ViperWorx/AX-02/Images/AX-02_2.png

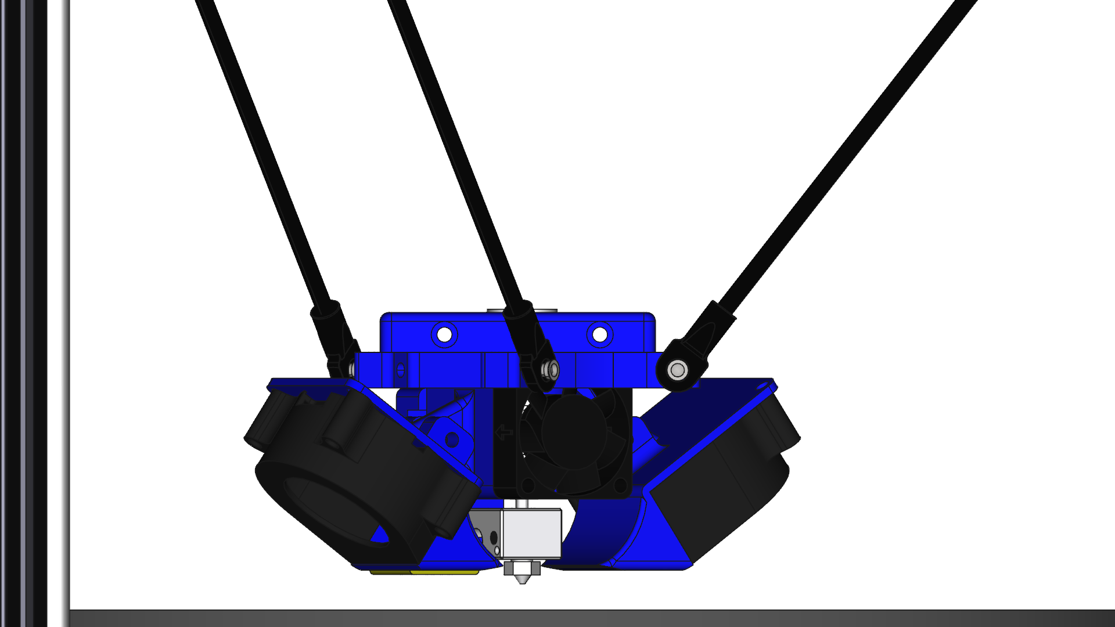
Images/AX-02_2.png
