ViperWorx/AX-02/Images/AX-02_4.png

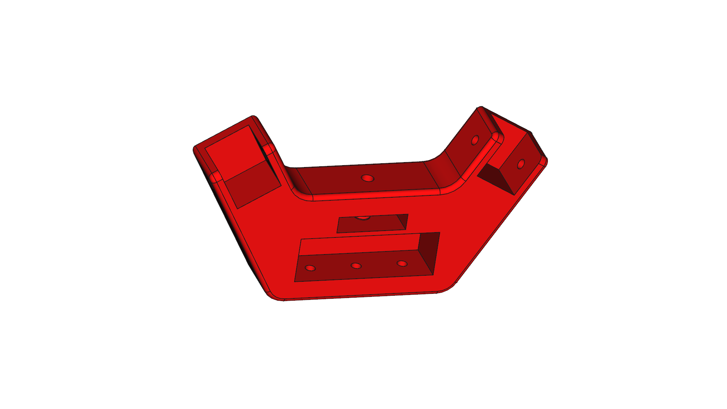
Images/AX-02_4.png
