ViperWorx/AX-02/FreeCAD/STEP/Hardware Parts/Build_plate.step

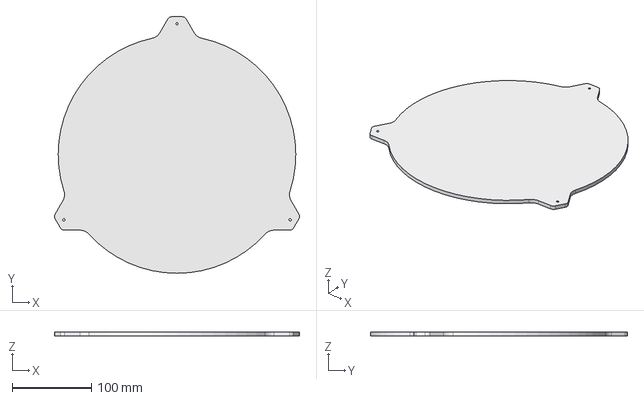
[picture p24: CAD file, 2017-04-28]
FreeCAD/STEP/Hardware Parts/Build_plate.step
309.3 x 323.9 x 5.00 mm
