ViperWorx/AX-02/FreeCAD/STEP/Printed Parts/Top_Bracket.step

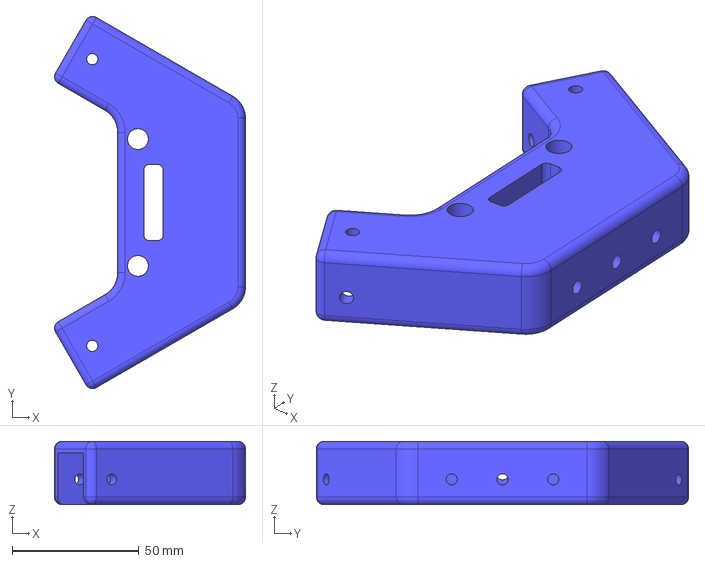
[picture p25: CAD file, 2017-02-15]
FreeCAD/STEP/Printed Parts/Top_Bracket.step
75.3 x 146.7 x 25.0 mm
