ViperWorx/AX-02/Cover_Plate.dxf

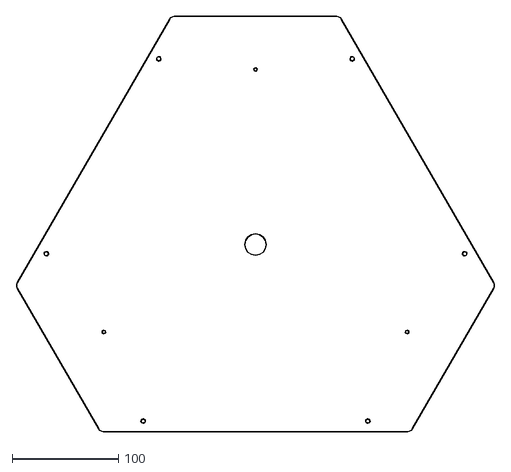
[picture p26: CAD file, 2017-04-28]
Cover_Plate.dxf
450.9 x 391.4
