ViperWorx/AX-02/FreeCAD/Arm_Tensioner.fcstd

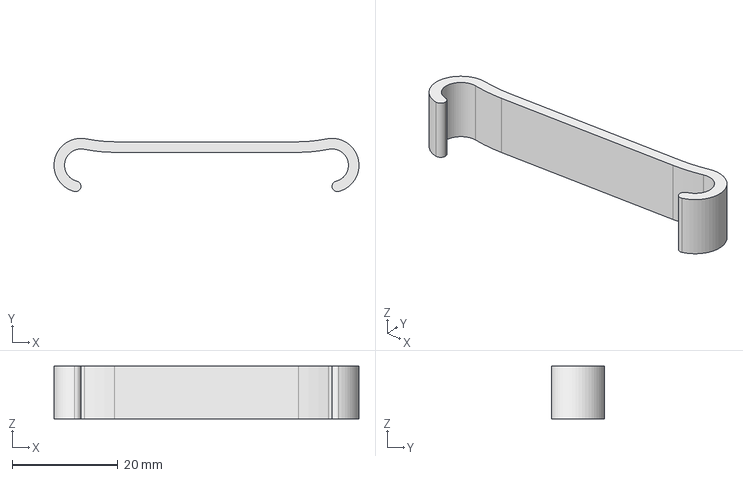
[picture p27: CAD file, 2017-03-06]
FreeCAD/Arm_Tensioner.fcstd
57.7 x 10.1 x 10.0 mm
