ViperWorx/AX-02/FreeCAD/STEP/Printed Parts/Layer_Fan_Mount.step

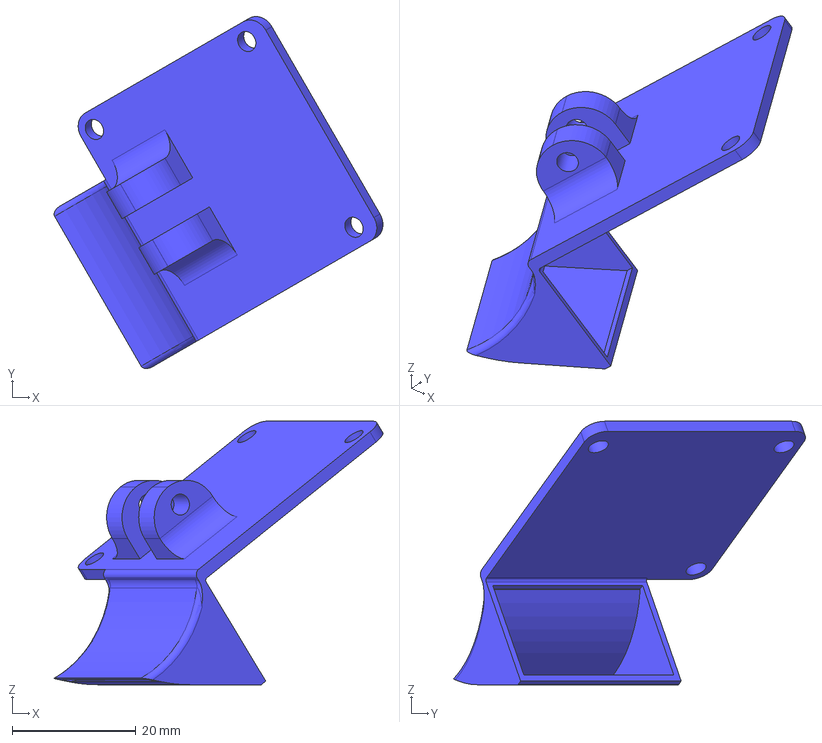
[picture p28: CAD file, 2017-01-31]
FreeCAD/STEP/Printed Parts/Layer_Fan_Mount.step
53.2 x 56.9 x 42.6 mm
