ViperWorx/AX-02/1_Effector.stl

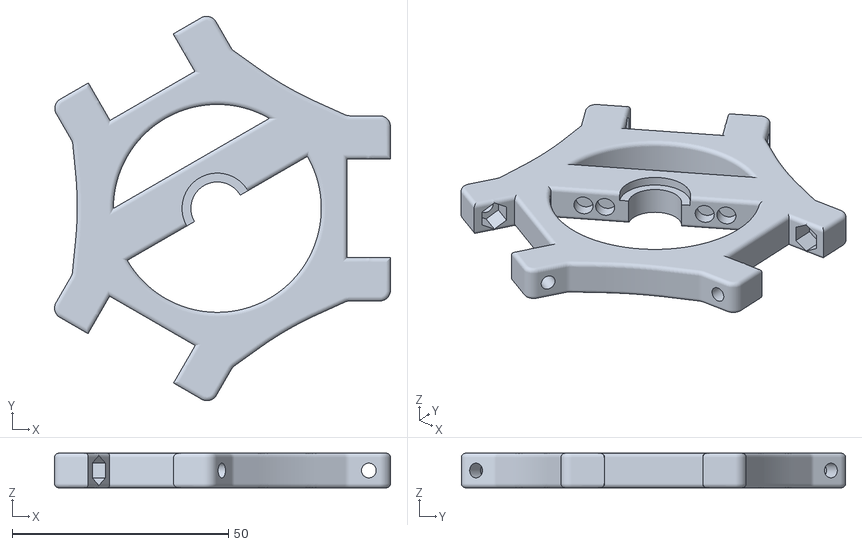
[picture p29: CAD file, 2017-03-30]
1_Effector.stl
77.6 x 88.8 x 8.00
