ViperWorx/AX-02/FreeCAD/Electronics_Plate_Bracket.fcstd

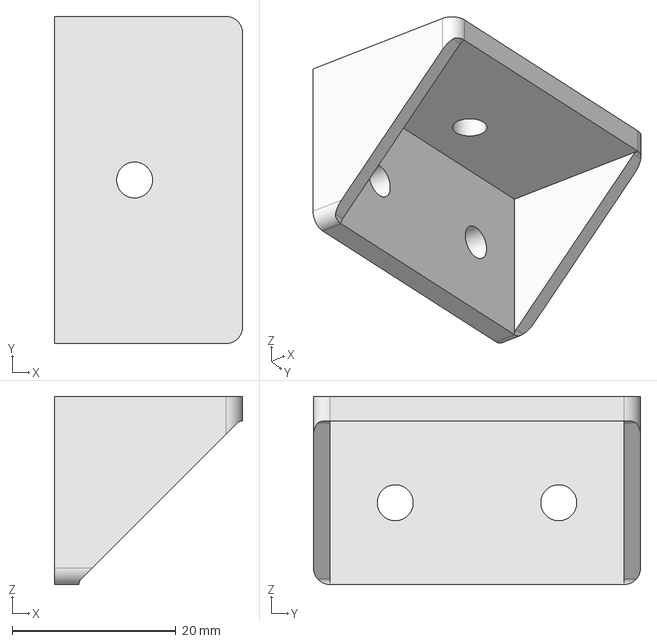
[picture p30: CAD file, 2017-03-06]
FreeCAD/Electronics_Plate_Bracket.fcstd
23.0 x 40.0 x 23.0 mm
