ViperWorx/AX-02/FreeCAD/STEP/Hardware Parts/Cover_Plate.step

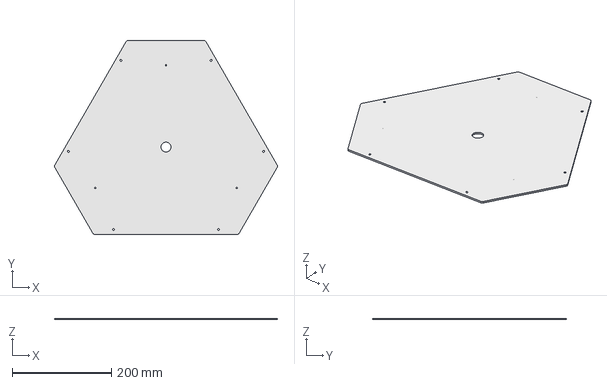
[picture p31: CAD file, 2017-04-28]
FreeCAD/STEP/Hardware Parts/Cover_Plate.step
450.4 x 391.4 x 3.00 mm
