ViperWorx/AX-02/FreeCAD/STEP/Printed Parts/Carriage.step

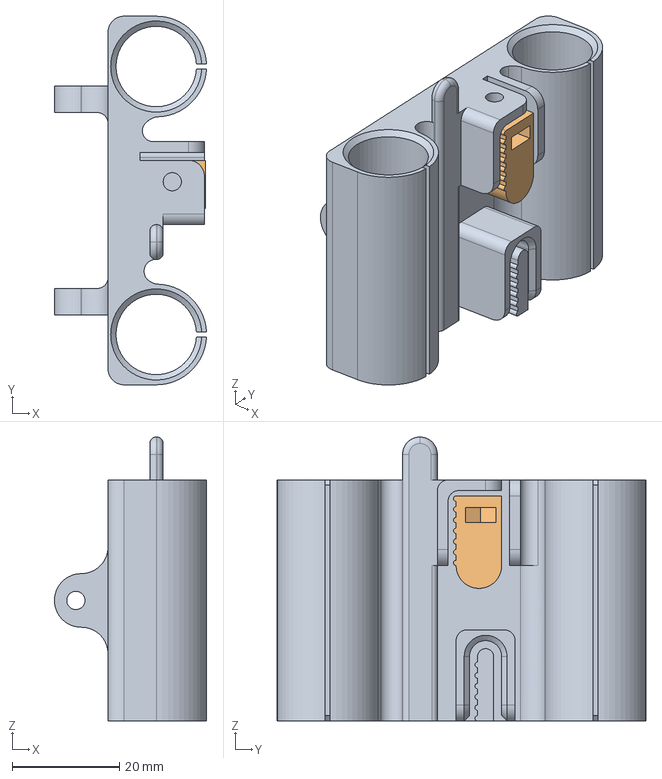
[picture p32: CAD file, 2017-01-22]
FreeCAD/STEP/Printed Parts/Carriage.step
28.4 x 68.8 x 53.0 mm
Carriage
Belt_Tensioner
