ViperWorx/AX-02/FreeCAD/Bowden_Tube_ Wire_Bundle_Clip.fcstd

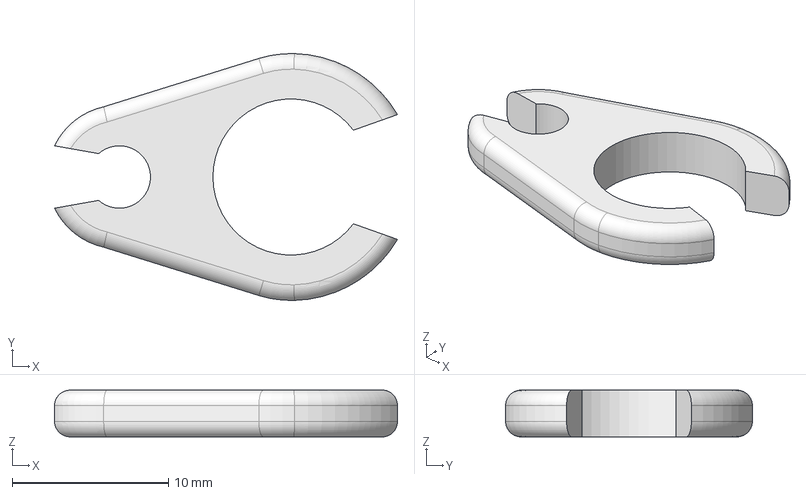
[picture p33: CAD file, 2017-02-25]
FreeCAD/Bowden_Tube_ Wire_Bundle_Clip.fcstd
22.0 x 15.8 x 3.00 mm
