ViperWorx/AX-02/FreeCAD/STEP/Printed Parts/Endstop_mount.step

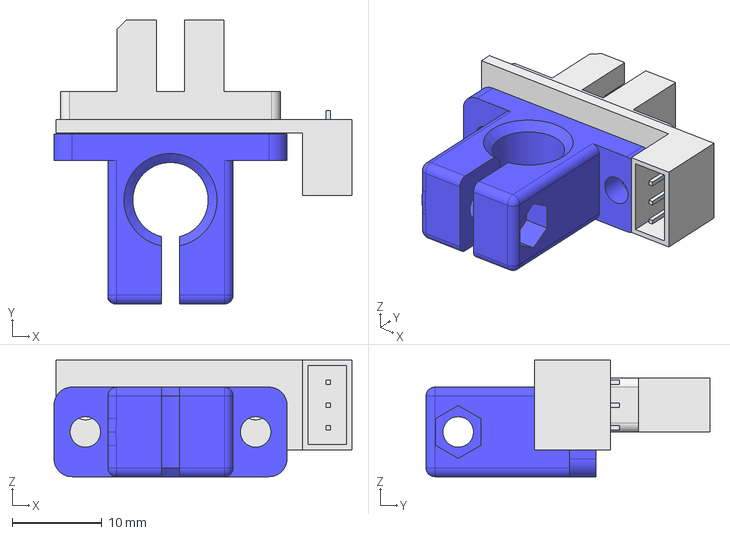
[picture p34: CAD file, 2017-01-22]
FreeCAD/STEP/Printed Parts/Endstop_mount.step
33.2 x 31.7 x 13.0 mm
Optical_Endstop
Endstop_Mount_Final
