ViperWorx/AX-02/FreeCAD/STEP/Hardware Parts/2060_3.step

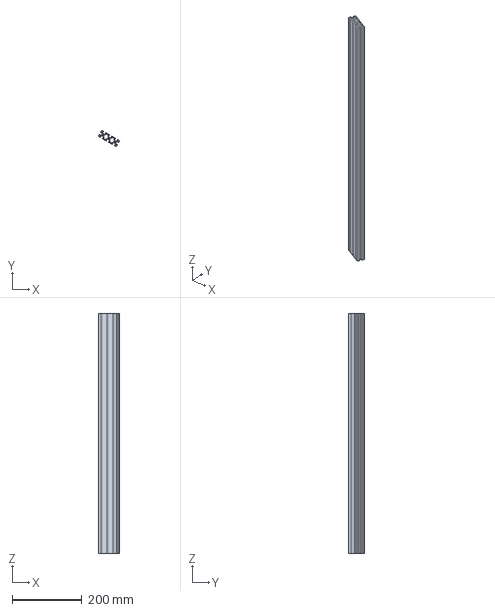
[picture p35: CAD file, 2017-02-15]
FreeCAD/STEP/Hardware Parts/2060_3.step
61.2 x 46.6 x 690.0 mm
