ViperWorx/AX-02/FreeCAD/STEP/Printed Parts/Mini_Viki_Case.step

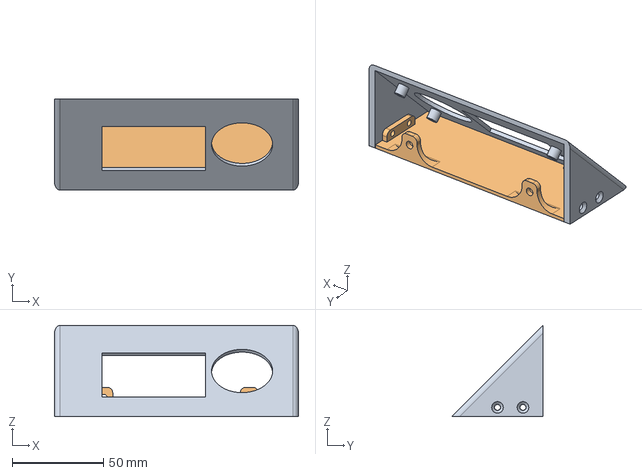
[picture p36: CAD file, 2017-01-22]
FreeCAD/STEP/Printed Parts/Mini_Viki_Case.step
134.0 x 50.0 x 50.0 mm
Base
