ViperWorx/AX-02/FreeCAD/Wire_Bundle_Clip.fcstd

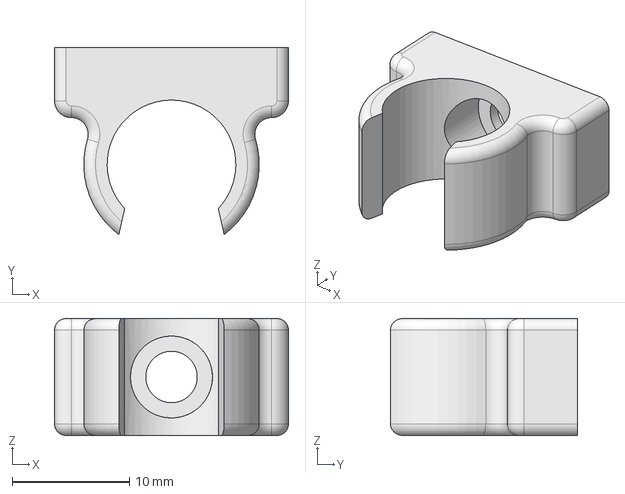
[picture p37: CAD file, 2017-02-25]
FreeCAD/Wire_Bundle_Clip.fcstd
20.0 x 16.0 x 10.0 mm
