ViperWorx/AX-02/FreeCAD/Dual_30mm_Fan Bracket.fcstd

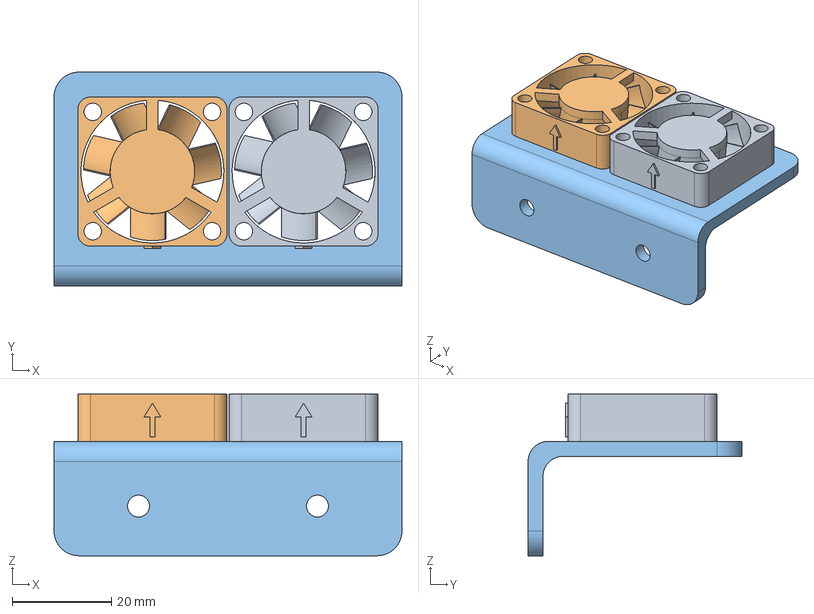
[picture p38: CAD file, 2017-02-23]
FreeCAD/Dual_30mm_Fan Bracket.fcstd
70.0 x 43.0 x 32.5 mm
