ViperWorx/AX-02/FreeCAD/STEP/Hardware Parts/2060_1.step

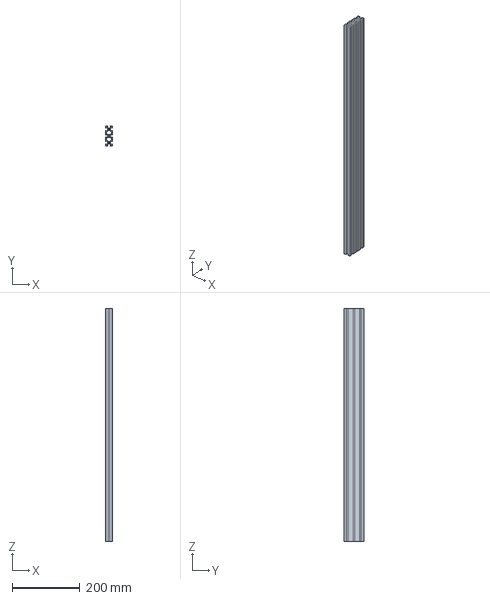
[picture p39: CAD file, 2017-02-15]
FreeCAD/STEP/Hardware Parts/2060_1.step
20.0 x 60.0 x 690.0 mm
