ViperWorx/AX-02/FreeCAD/8mm_Bush.fcstd

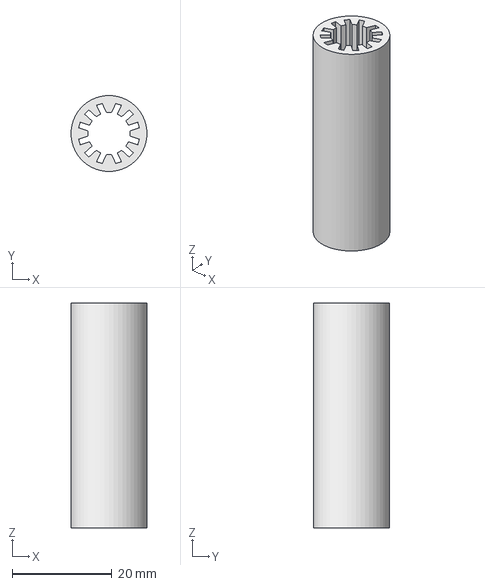
[picture p40: CAD file, 2017-02-15]
FreeCAD/8mm_Bush.fcstd
15.2 x 15.2 x 45.0 mm
