ViperWorx/AX-02/FreeCAD/STEP/Hardware Parts/2040_1.step

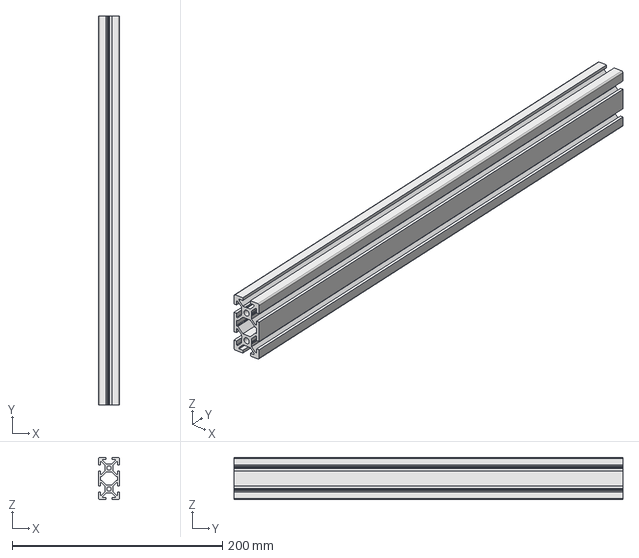
[picture p41: CAD file, 2017-02-15]
FreeCAD/STEP/Hardware Parts/2040_1.step
20.0 x 370.0 x 40.0 mm
