ViperWorx/AX-02/FreeCAD/IEC case.fcstd

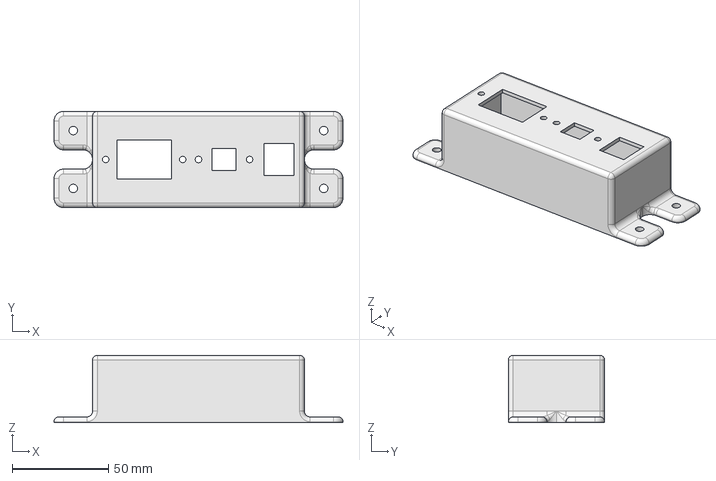
[picture p42: CAD file, 2017-02-08]
FreeCAD/IEC case.fcstd
150.0 x 50.0 x 35.0 mm
