ViperWorx/AX-02/FreeCAD/STEP/Hardware Parts/2020_1.step

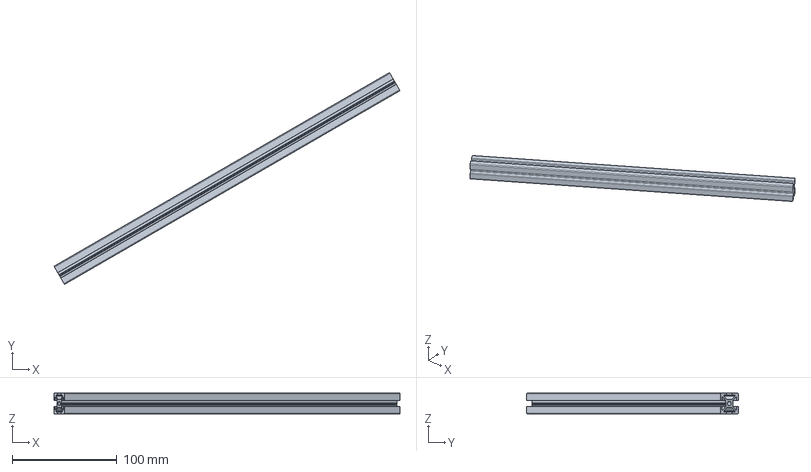
[picture p43: CAD file, 2017-02-15]
FreeCAD/STEP/Hardware Parts/2020_1.step
330.4 x 202.3 x 20.0 mm
