ViperWorx/AX-02/FreeCAD/AX-02_Logo_3D.fcstd

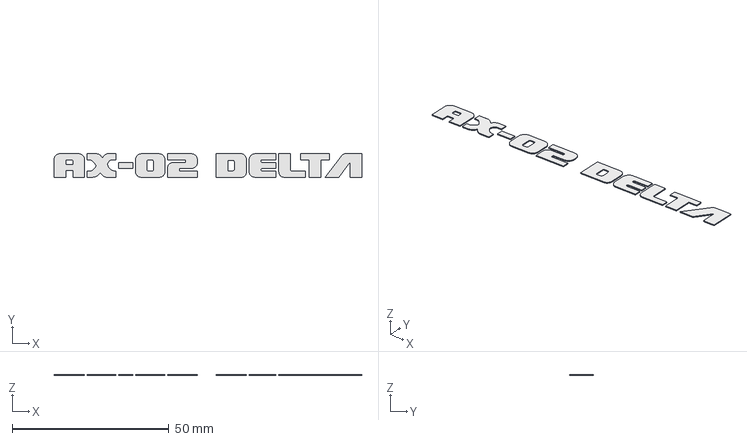
[picture p44: CAD file, 2017-02-03]
FreeCAD/AX-02_Logo_3D.fcstd
98.3 x 7.55 x 0.28 mm
