ViperWorx/AX-02/1_Dual_30mm_Fan_Bracket-Board_Cooler.stl

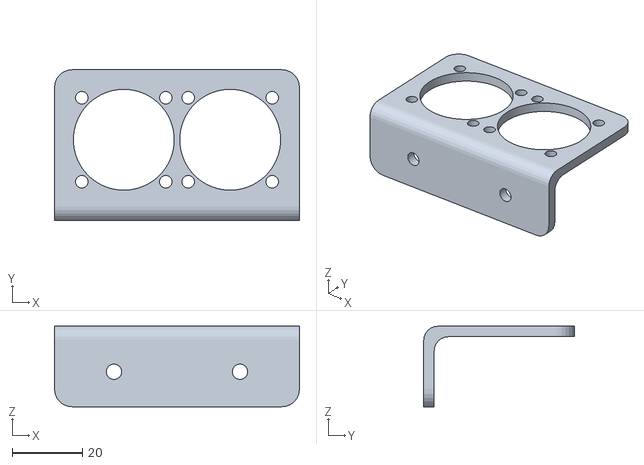
[picture p45: CAD file, 2017-02-23]
1_Dual_30mm_Fan_Bracket-Board_Cooler.stl
70.0 x 43.0 x 23.0
