ViperWorx/AX-02/FreeCAD/Mini Viki Screen Mount.fcstd

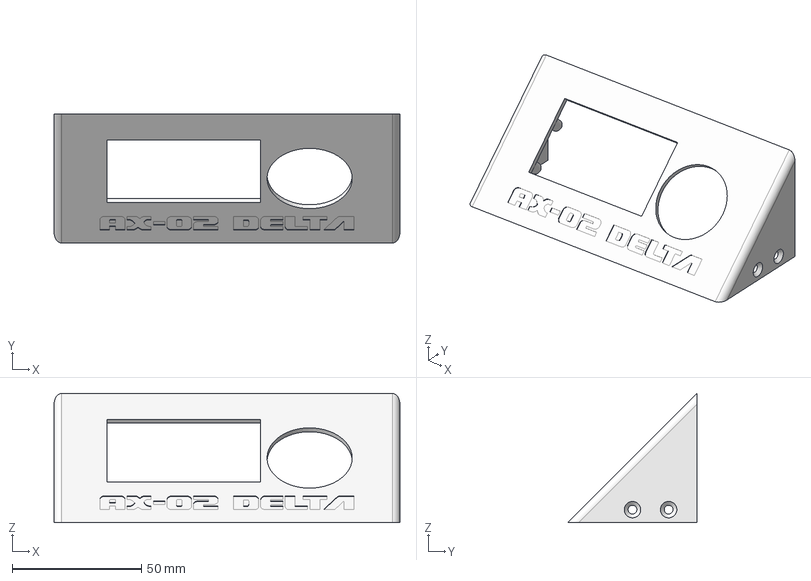
[picture p46: CAD file, 2017-02-03]
FreeCAD/Mini Viki Screen Mount.fcstd
134.0 x 50.0 x 50.0 mm
