ViperWorx/AX-02/FreeCAD/STEP/Hardware Parts/IEC Socket.stp

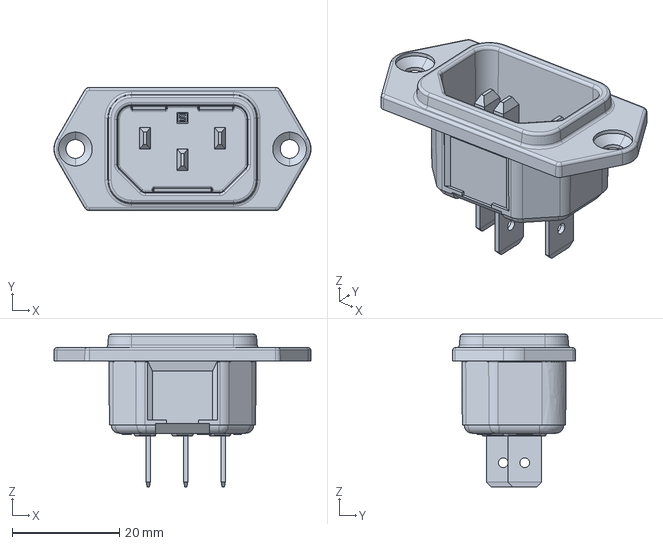
[picture p47: CAD file, 2017-01-22]
FreeCAD/STEP/Hardware Parts/IEC Socket.stp
48.0 x 23.0 x 28.5 mm
