ViperWorx/AX-02/3_Carriage.stl

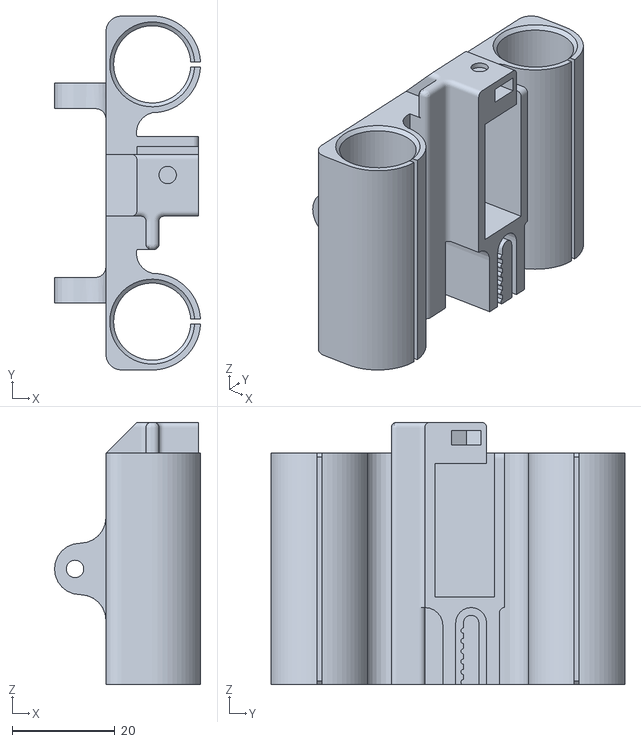
[picture p48: CAD file, 2017-02-23]
3_Carriage.stl
28.4 x 68.8 x 51.0
