ViperWorx/AX-02/FreeCAD/STEP/Hardware Parts/Optical endstop v3.step

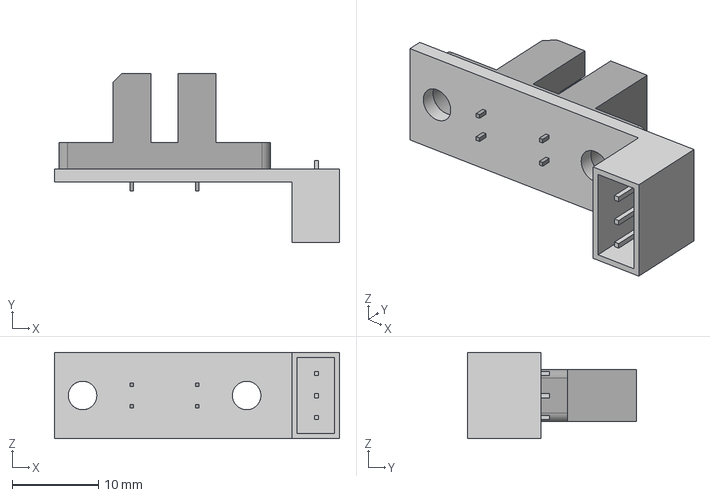
[picture p49: CAD file, 2017-01-17]
FreeCAD/STEP/Hardware Parts/Optical endstop v3.step
33.0 x 19.6 x 10.0 mm
