ViperWorx/AX-02/FreeCAD/STEP/Hardware Parts/SN04-N.STEP

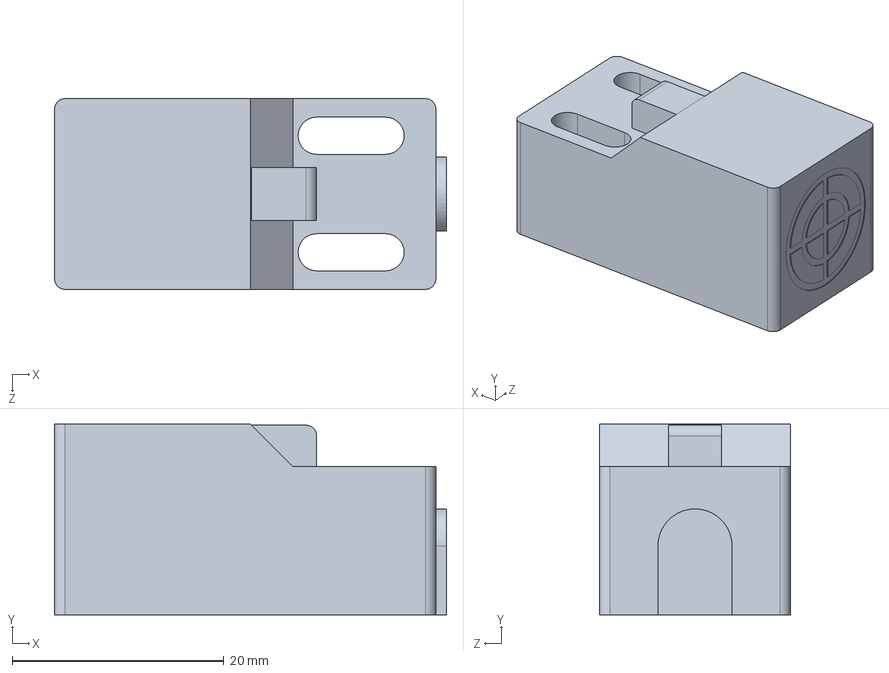
[picture p50: CAD file, 2017-01-17]
FreeCAD/STEP/Hardware Parts/SN04-N.STEP
37.0 x 18.0 x 18.0 mm
