ViperWorx/AX-02/FreeCAD/STEP/Hardware Parts/blower_fan.STEP

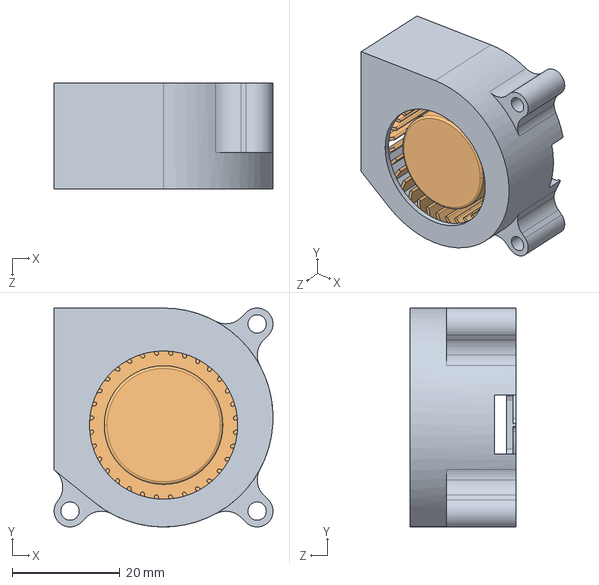
[picture p51: CAD file, 2017-01-15]
FreeCAD/STEP/Hardware Parts/blower_fan.STEP
40.6 x 40.6 x 19.6 mm
