ViperWorx/AX-02/FreeCAD/STEP/Hardware Parts/e3d_v6_175.stp

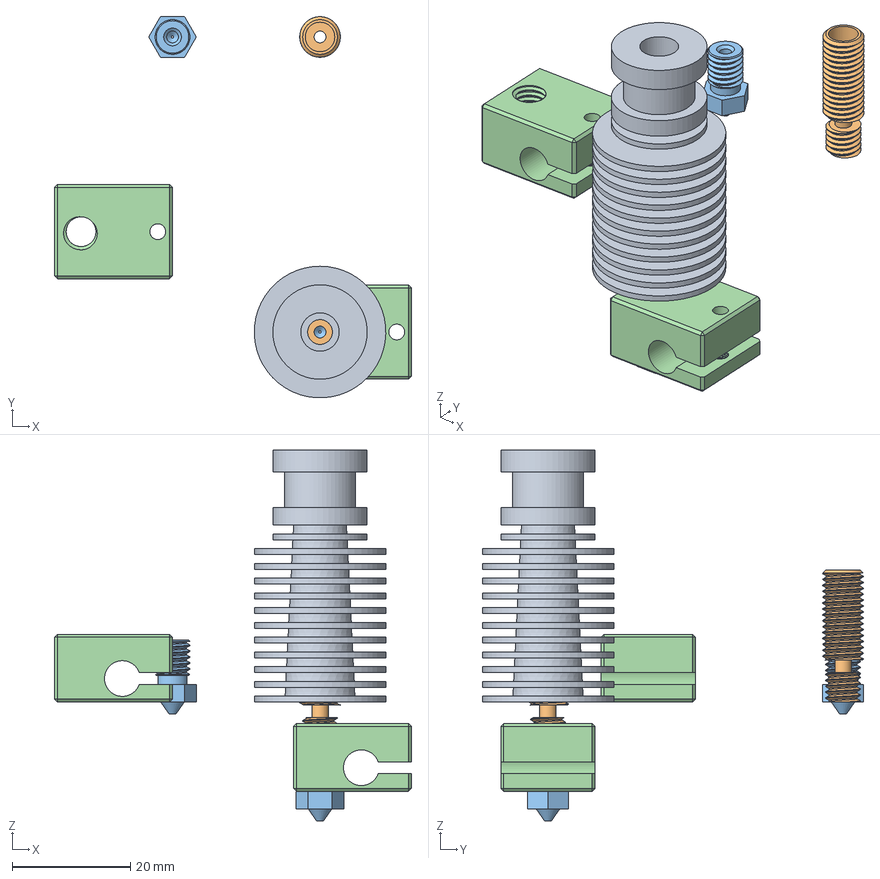
[picture p52: CAD file, 2017-01-15]
FreeCAD/STEP/Hardware Parts/e3d_v6_175.stp
60.5 x 64.6 x 62.8 mm
