ViperWorx/AX-02/3_Belt_Tensioner.stl

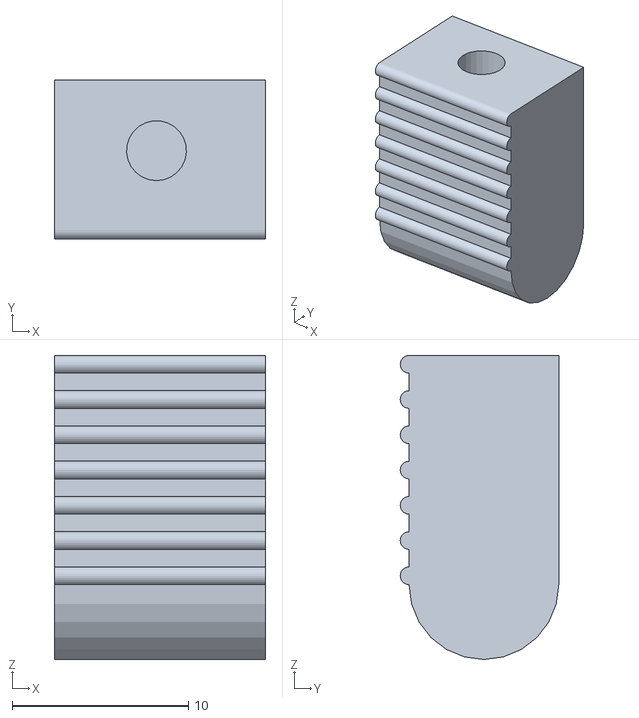
[picture p53: CAD file, 2017-02-06]
3_Belt_Tensioner.stl
12.0 x 9.00 x 17.2
