ViperWorx/AX-02/3_Endstop_Mount.stl

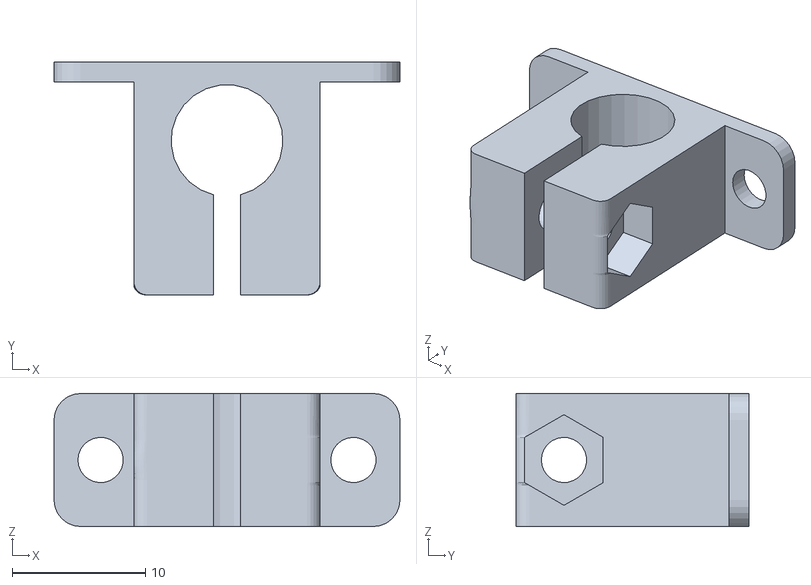
[picture p54: CAD file, 2017-02-05]
3_Endstop_Mount.stl
26.0 x 17.5 x 10.0
