ViperWorx/AX-02/1_Hot_End_Clamp.stl

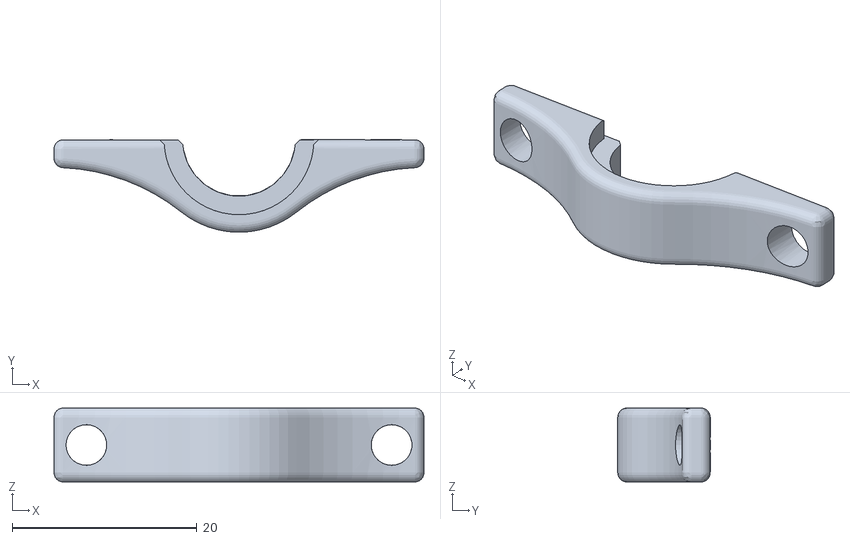
[picture p55: CAD file, 2017-02-05]
1_Hot_End_Clamp.stl
40.0 x 10.0 x 8.00
