ViperWorx/AX-02/FreeCAD/STEP/Hardware Parts/NFS5-2020-370_2_03.stp

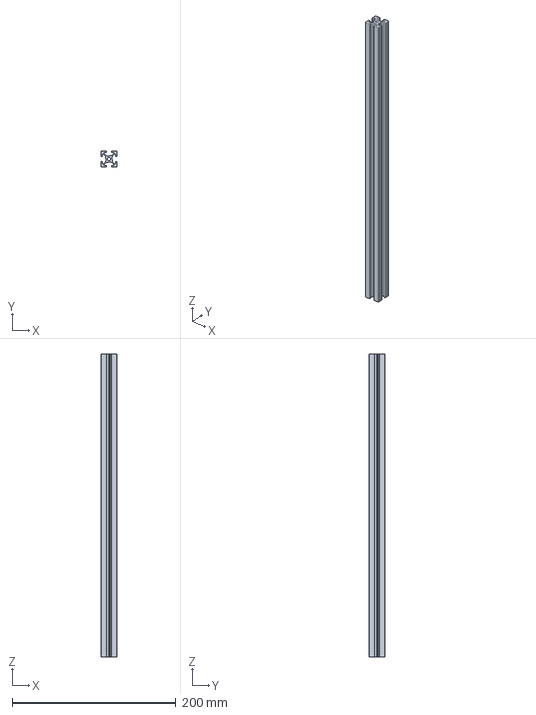
[picture p56: CAD file, 2017-01-15]
FreeCAD/STEP/Hardware Parts/NFS5-2020-370_2_03.stp
20.0 x 20.0 x 370.0 mm
