ViperWorx/AX-02/1_Mini_Viki_Case_Front.stl

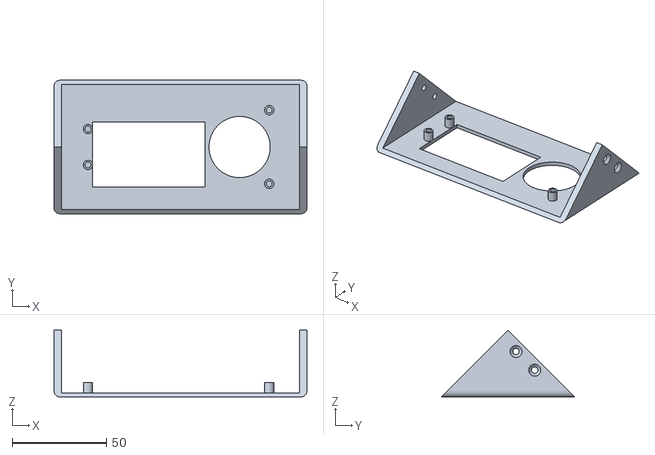
[picture p57: CAD file, 2017-02-03]
1_Mini_Viki_Case_Front.stl
134.0 x 70.7 x 35.4
