ViperWorx/AX-02/FreeCAD/STEP/Hardware Parts/30mm Fan.step

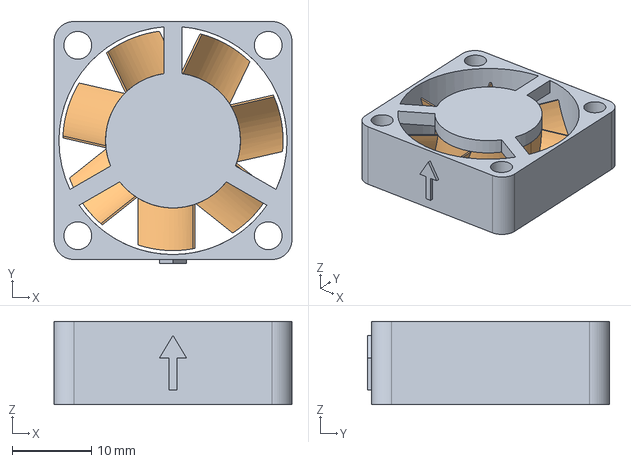
[picture p58: CAD file, 2017-01-15]
FreeCAD/STEP/Hardware Parts/30mm Fan.step
30.0 x 30.5 x 10.5 mm
