ViperWorx/AX-02/1_Mini_Viki_Case_Front_Logo.stl

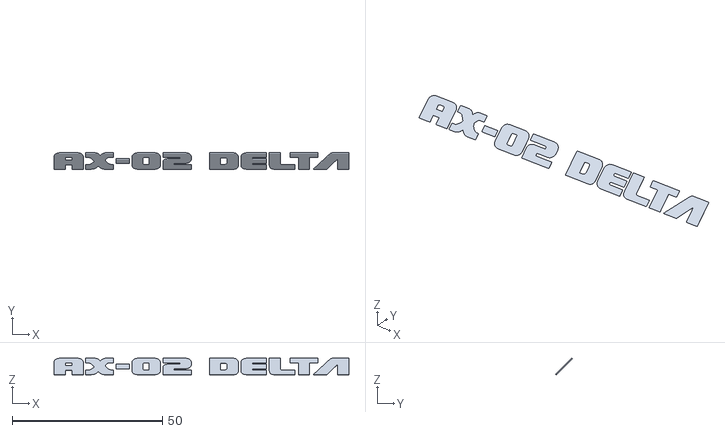
[picture p59: CAD file, 2017-02-03]
1_Mini_Viki_Case_Front_Logo.stl
98.3 x 5.54 x 5.54
