ViperWorx/AX-02/FreeCAD/STEP/Hardware Parts/PM Wantai 609  Nema 17.stp

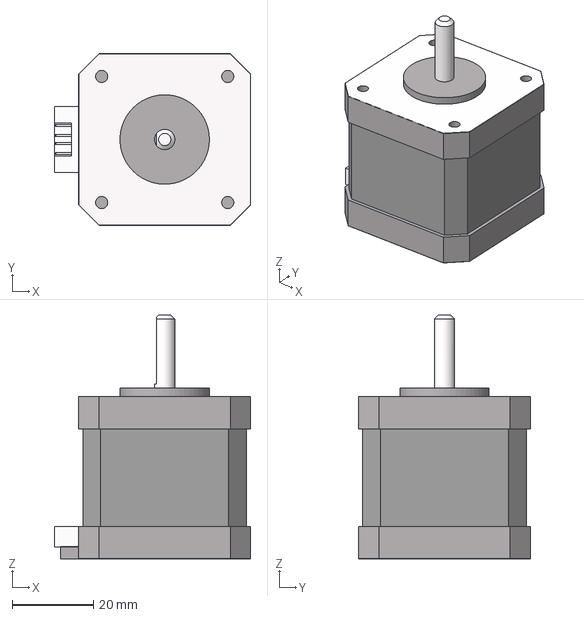
[picture p60: CAD file, 2017-01-15]
FreeCAD/STEP/Hardware Parts/PM Wantai 609 Nema 17.stp
48.3 x 42.3 x 60.0 mm
