ViperWorx/AX-02/AX-02_Logo.dxf

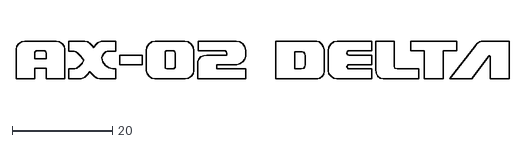
[picture p61: CAD file, 2017-02-03]
AX-02_Logo.dxf
98.3 x 7.55
