ViperWorx/AX-02/FreeCAD/STEP/Hardware Parts/Traxxas 5347 ball joint.stp

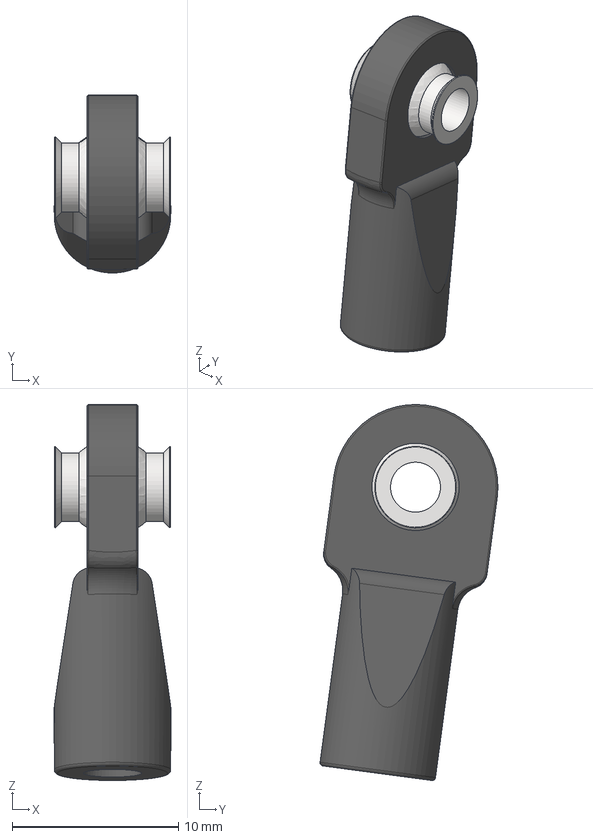
[picture p62: CAD file, 2017-01-15]
FreeCAD/STEP/Hardware Parts/Traxxas 5347 ball joint.stp
7.00 x 10.7 x 22.6 mm
