ViperWorx/AX-02/FreeCAD/STEP/Hardware Parts/40mm_fan.stp

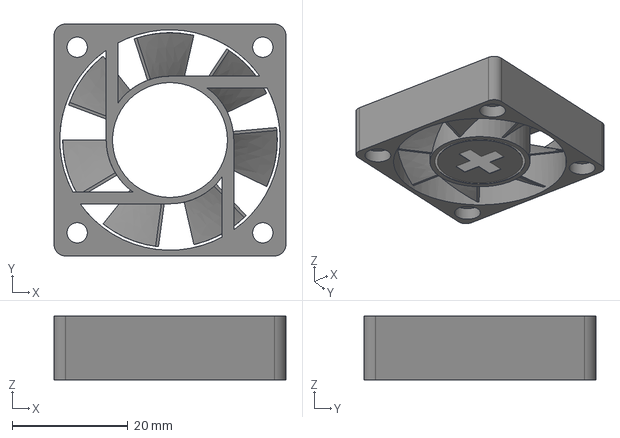
[picture p63: CAD file, 2017-01-15]
FreeCAD/STEP/Hardware Parts/40mm_fan.stp
40.0 x 40.0 x 11.0 mm
