ViperWorx/AX-02/1_Mini_Viki_Case_Base.stl

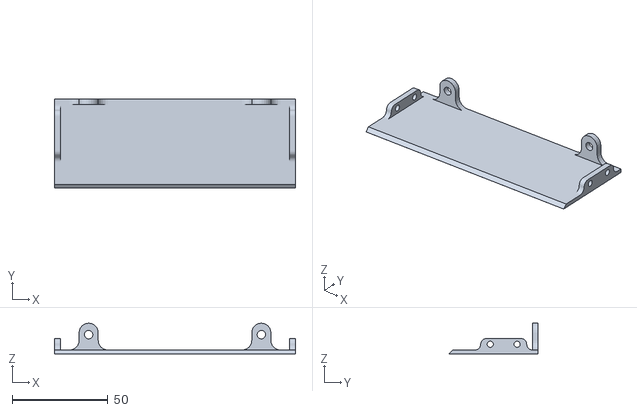
[picture p64: CAD file, 2017-02-03]
1_Mini_Viki_Case_Base.stl
125.6 x 46.6 x 16.0
