ViperWorx/AX-02/2_Layer_Fan Mount.stl

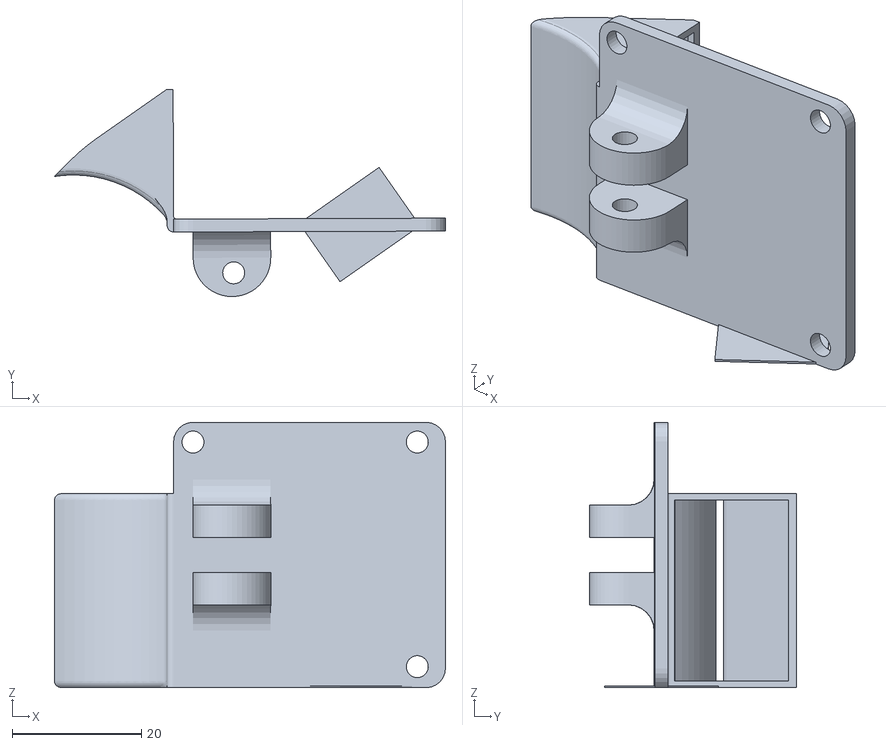
[picture p65: CAD file, 2017-02-03]
2_Layer_Fan Mount.stl
60.4 x 32.0 x 41.0
