ViperWorx/AX-02/1_Hot_End_Fan_Housing.stl

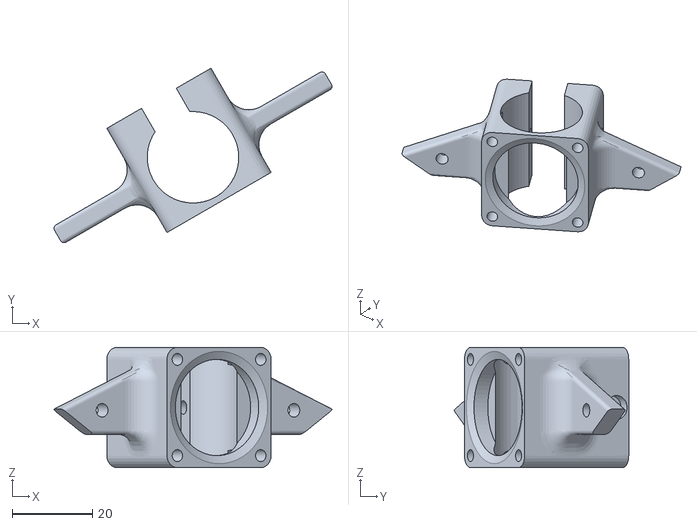
[picture p66: CAD file, 2017-01-31]
1_Hot_End_Fan_Housing.stl
69.3 x 43.5 x 30.0
